svenpetersen1965/Atari-XL-XE-A-V-Adapter/Atari_AV_Adapter/Rev. 0/pictures/AV-Adapter in case #1.jpg

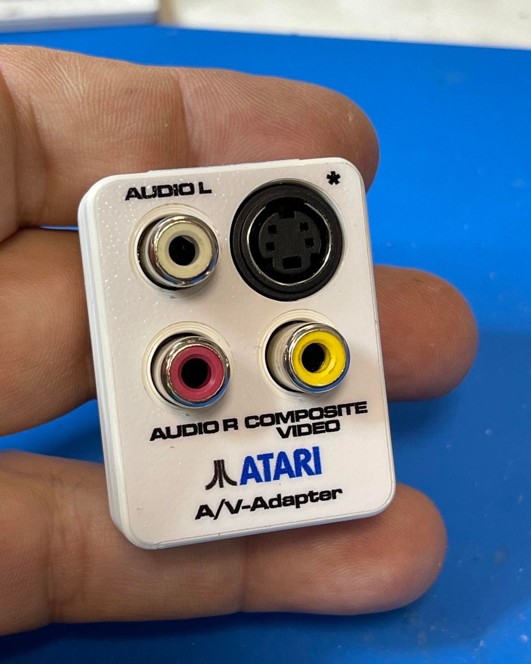
Atari_AV_Adapter/Rev. 0/pictures/AV-Adapter in case #1.jpg
