svenpetersen1965/Atari-XL-XE-A-V-Adapter/Atari_AV_Adapter/Rev. 0/pictures/PCB_top.jpg

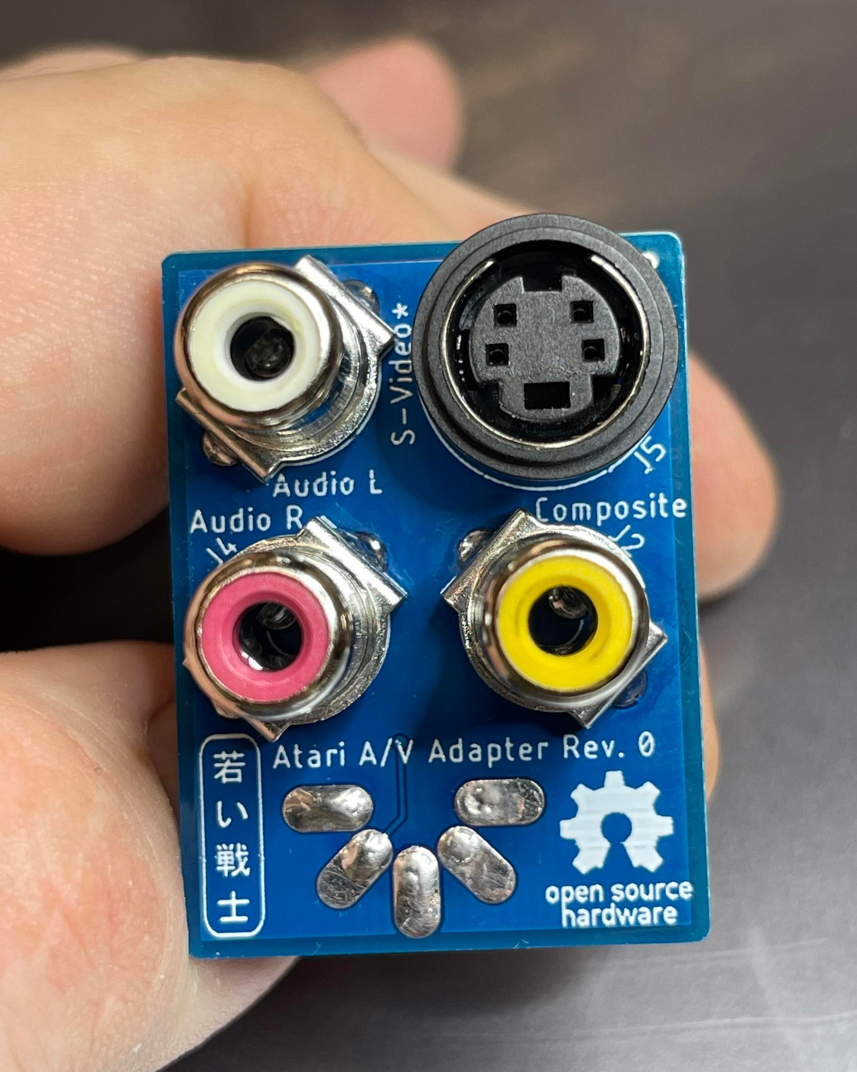
Atari_AV_Adapter/Rev. 0/pictures/PCB_top.jpg
