svenpetersen1965/Atari-XL-XE-A-V-Adapter/Atari_AV_Adapter/Rev. 1/pictures/2985_-_LUM_SV-50_TOP.JPG

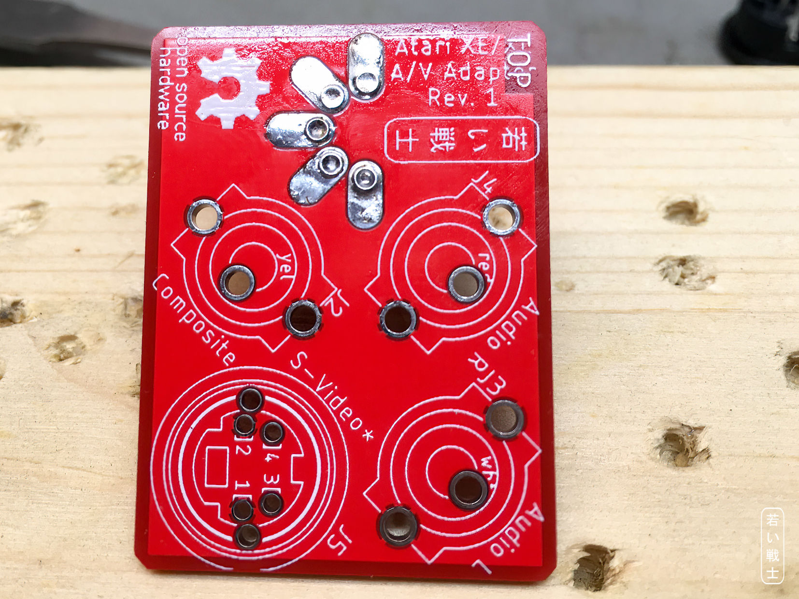
Atari_AV_Adapter/Rev. 1/pictures/2985_-_LUM_SV-50_TOP.JPG
