svenpetersen1965/Atari-XL-XE-A-V-Adapter/Atari_AV_Adapter/Rev. 1/pictures/3087_-_fitting_800XL.JPG

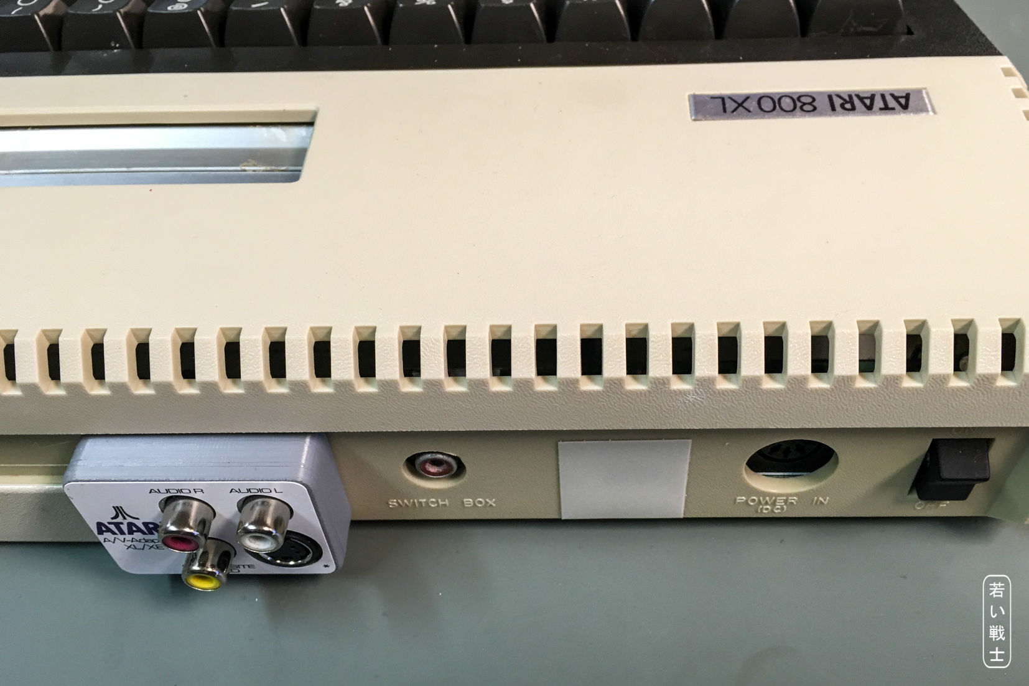
Atari_AV_Adapter/Rev. 1/pictures/3087_-_fitting_800XL.JPG
