svenpetersen1965/Atari-XL-XE-A-V-Adapter/Atari_AV_Adapter/Rev. 1/pictures/Fitting_800XE.jpg

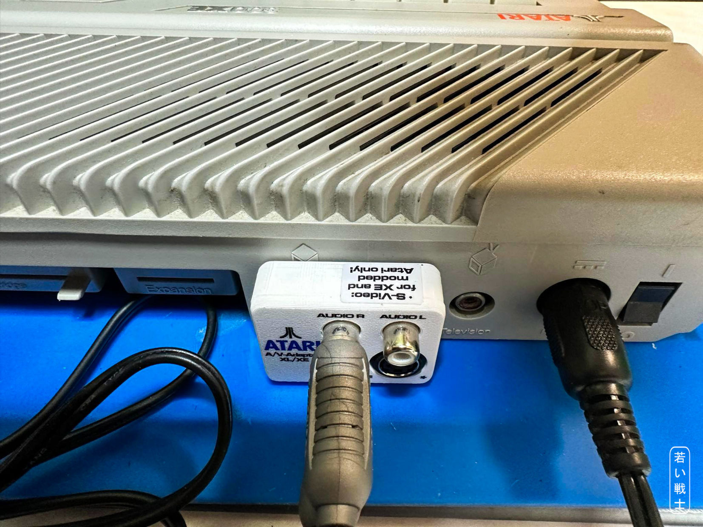
Atari_AV_Adapter/Rev. 1/pictures/Fitting_800XE.jpg
