svenpetersen1965/Atari-XL-XE-A-V-Adapter/Atari_AV_Adapter/Rev. 0/pictures/Testfit_130XE.jpg

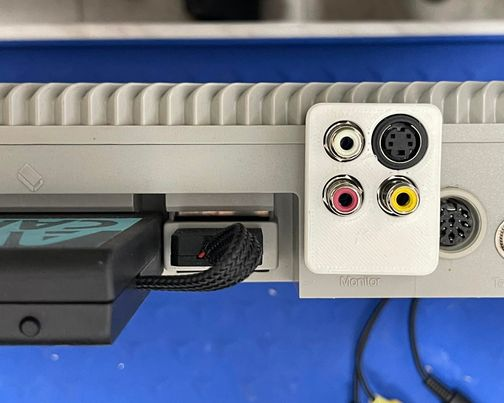
Atari_AV_Adapter/Rev. 0/pictures/Testfit_130XE.jpg
