svenpetersen1965/Atari-XL-XE-A-V-Adapter/Atari_AV_Adapter/Rev. 0/pictures/Testfit_800XL_side.jpg

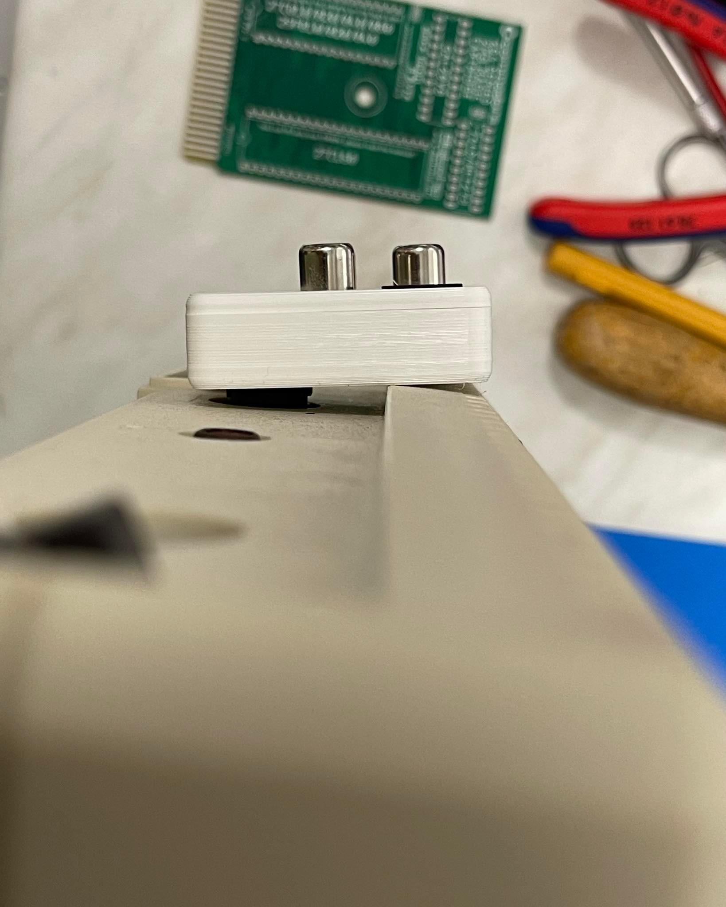
Atari_AV_Adapter/Rev. 0/pictures/Testfit_800XL_side.jpg
